gdampf/uTerm/STM32F030F4/Hardware/LT Spice Simulation/video buffer.asc

C1: cap; 22pF
C2: polcap; 10µ; V=6.3 Irms=0 Rser=10 Lser=0
Q1: npn3; 2N3904
R1: res; 75R
R2: res; 200R
R3: res; 1k
R4: res; 475R
R5: res; 2K
V1: voltage; 3.3V; Rser=1R
V2: voltage; PULSE(0 3.3V 0 4ns 4ns 16ns 40ns); Rser=33r
Named nets: 0
.tran 100ns
