gdampf/uTerm/STM32F030F4/Firmware/ChibiTerm/vga16.fnt.c

  // vga16.fnt
  // 0x00
  0x00,0x00,0x00,0x00,0x00,0x00,0x00,0x00,0x00,0x00,0x00,0x00,0x00,0x00,0x00,0x00,
  // 0x01
  0x55,0xaa,0x55,0xaa,0x55,0xaa,0x55,0xaa,0x55,0xaa,0x55,0xaa,0x55,0xaa,0x55,0xaa,
  // 0x02
  0x00,0x00,0x00,0x00,0x00,0xfe,0xfe,0xfe,0xfe,0xfe,0xfe,0x00,0x00,0x00,0x00,0x00,
  // 0x03
  0x00,0x00,0x00,0x00,0x00,0x00,0x00,0x00,0xff,0xff,0xff,0xff,0xff,0xff,0xff,0xff,
  // 0x04
  0xff,0xff,0xff,0xff,0xff,0xff,0xff,0xff,0x00,0x00,0x00,0x00,0x00,0x00,0x00,0x00,
  // 0x05
  0x00,0x00,0x00,0x00,0x10,0x10,0x38,0x38,0x7c,0x7c,0xfe,0xfe,0x00,0x00,0x00,0x00,
  // 0x06
  0x00,0x00,0x00,0x00,0xfe,0xfe,0x7c,0x7c,0x38,0x38,0x10,0x10,0x00,0x00,0x00,0x00,
  // 0x07
  0x00,0x00,0x00,0x04,0x0c,0x1c,0x3c,0x7c,0x3c,0x1c,0x0c,0x04,0x00,0x00,0x00,0x00,
  // 0x08
  0x00,0x00,0x00,0x40,0x60,0x70,0x78,0x7c,0x78,0x70,0x60,0x40,0x00,0x00,0x00,0x00,
  // 0x09
  0x00,0x00,0x00,0x00,0xfe,0x00,0x00,0xfe,0x00,0x00,0xfe,0x00,0x00,0x00,0x00,0x00,
  // 0x0a
  0x18,0x18,0x18,0x18,0x18,0x18,0x18,0xf8,0x00,0x00,0x00,0x00,0x00,0x00,0x00,0x00,
  // 0x0b
  0x00,0x00,0x00,0x00,0x00,0x00,0x00,0xf8,0x18,0x18,0x18,0x18,0x18,0x18,0x18,0x18,
  // 0x0c
  0x00,0x00,0x00,0x00,0x00,0x00,0x00,0x1f,0x18,0x18,0x18,0x18,0x18,0x18,0x18,0x18,
  // 0x0d
  0x18,0x18,0x18,0x18,0x18,0x18,0x18,0x1f,0x00,0x00,0x00,0x00,0x00,0x00,0x00,0x00,
  // 0x0e
  0x18,0x18,0x18,0x18,0x18,0x18,0x18,0xff,0x18,0x18,0x18,0x18,0x18,0x18,0x18,0x18,
  // 0x0f
  0x00,0x18,0x3c,0x7e,0x18,0x18,0x18,0x18,0x18,0x18,0x18,0x18,0x18,0x00,0x00,0x00,
  // 0x10
  0x00,0x18,0x18,0x18,0x18,0x18,0x18,0x18,0x18,0x18,0x7e,0x3c,0x18,0x00,0x00,0x00,
  // 0x11
  0x00,0x00,0x00,0x00,0x00,0x00,0x00,0xff,0x00,0x00,0x00,0x00,0x00,0x00,0x00,0x00,
  // 0x12
  0x00,0x18,0x3c,0x7e,0x18,0x18,0x18,0x18,0x18,0x18,0x7e,0x3c,0x18,0x00,0x00,0x00,
  // 0x13
  0x00,0x00,0x00,0x00,0x00,0x00,0x18,0x18,0x18,0x00,0x00,0x00,0x00,0x00,0x00,0x00,
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
