gdampf/uTerm/STM32F030F4/Firmware/Matrix Clock Demo/fifo.h

#ifndef _FIFO_H_
#define _FIFO_H_

#include <stdint.h>
#include "vga-min.h"

typedef uint8_t FIFO_Data_t;
typedef uint8_t FIFO_Index_t;

typedef struct
{
	FIFO_Data_t 					*Buffer;
	FIFO_Index_t	 				SizeMask;	
	volatile FIFO_Index_t Head;
	volatile FIFO_Index_t Tail;
} FIFO;

#define FIFO_INC(INDEX,MOD1)	((INDEX+1)&(MOD1))

void    FIFO_Clear(FIFO *Queue);
uint8_t FIFO_Write(FIFO *Queue, FIFO_Data_t data);
uint8_t FIFO_WriteAvail(FIFO *Queue);
uint8_t FIFO_Read(FIFO *Queue, FIFO_Data_t *data);
uint8_t FIFO_ReadAvail(FIFO *Queue);
uint8_t Getc(FIFO *Queue);
uint8_t Getc_Timeout(FIFO *Queue, FIFO_Data_t *data, uint16_t Timeout);

#endif
